SeryiBaran/ardustat/src/main.h

#pragma once

#include <Arduino.h>
#include <EEManager.h>
#include <EncButton.h>
#include <GyverNTC.h>
#include <GyverSegment.h>
#include <PinChangeInterrupt.h>
#include <TimerMs.h>

#include "config.h"
